Digital-Naturalism-Laboratories/Mothbox_Electronics/Mothbox_PCBs/Mothbox_PCB_5.0.6/MothBox/Adafruit-INA219-Current-Sensor-PCB-master/assets/904.jpg

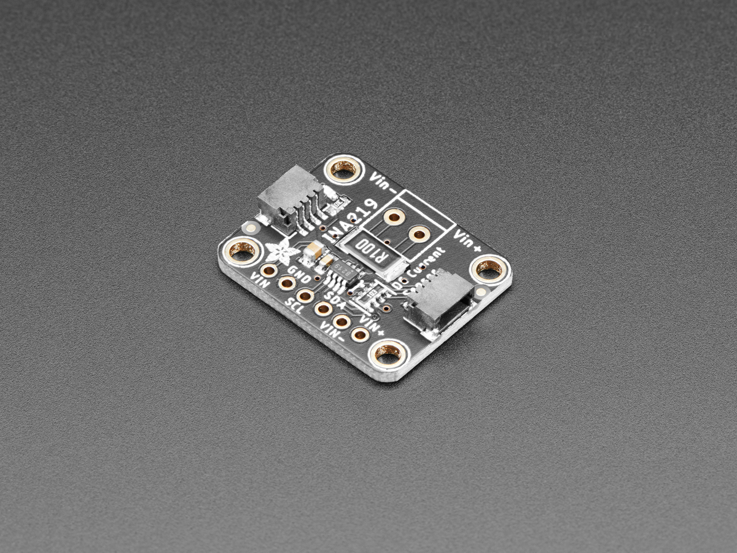
Mothbox_PCBs/Mothbox_PCB_5.0.6/MothBox/Adafruit-INA219-Current-Sensor-PCB-master/assets/904.jpg
