Digital-Naturalism-Laboratories/Mothbox_Electronics/Mothbox_PCBs/Mothbox_PCB_5.0.6/MothBox/graphics/FC5B0830.jpg

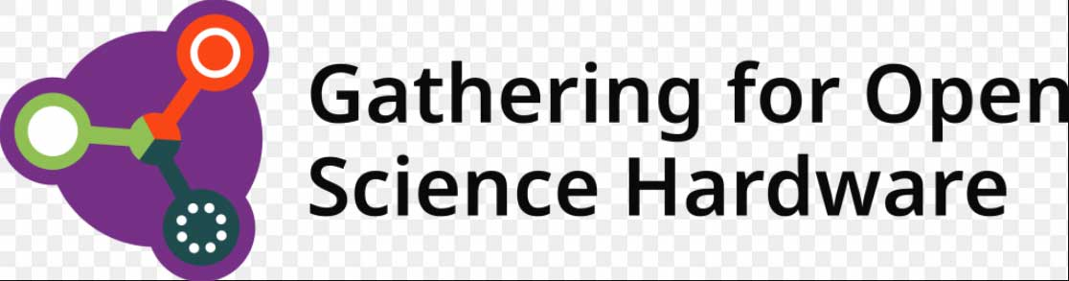
Mothbox_PCBs/Mothbox_PCB_5.0.6/MothBox/graphics/FC5B0830.jpg
