Digital-Naturalism-Laboratories/Mothbox_Electronics/Mothbox_PCBs/Mothbox_PCB_5.0.6/MothBox/Mothbox_5.0.4/MothBox_5.0.3/RPi5-HATplus-master/img/HATPlus_Template_dims.png

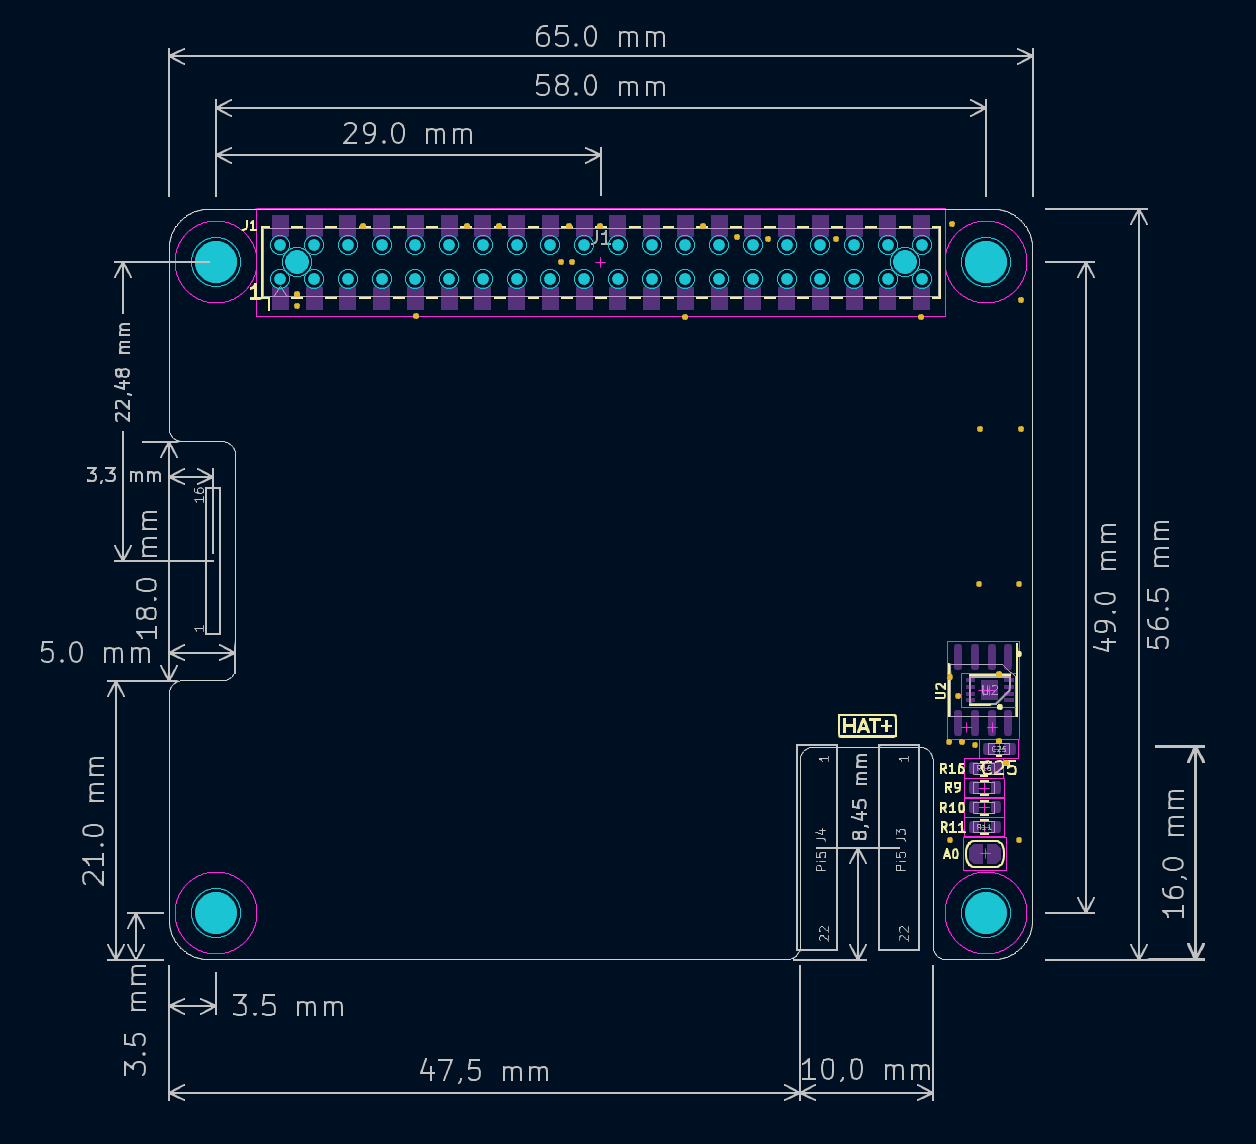
Mothbox_PCBs/Mothbox_PCB_5.0.6/MothBox/Mothbox_5.0.4/MothBox_5.0.3/RPi5-HATplus-master/img/HATPlus_Template_dims.png
