Digital-Naturalism-Laboratories/Mothbox_Electronics/Mothbox_PCBs/reference rotations b.png

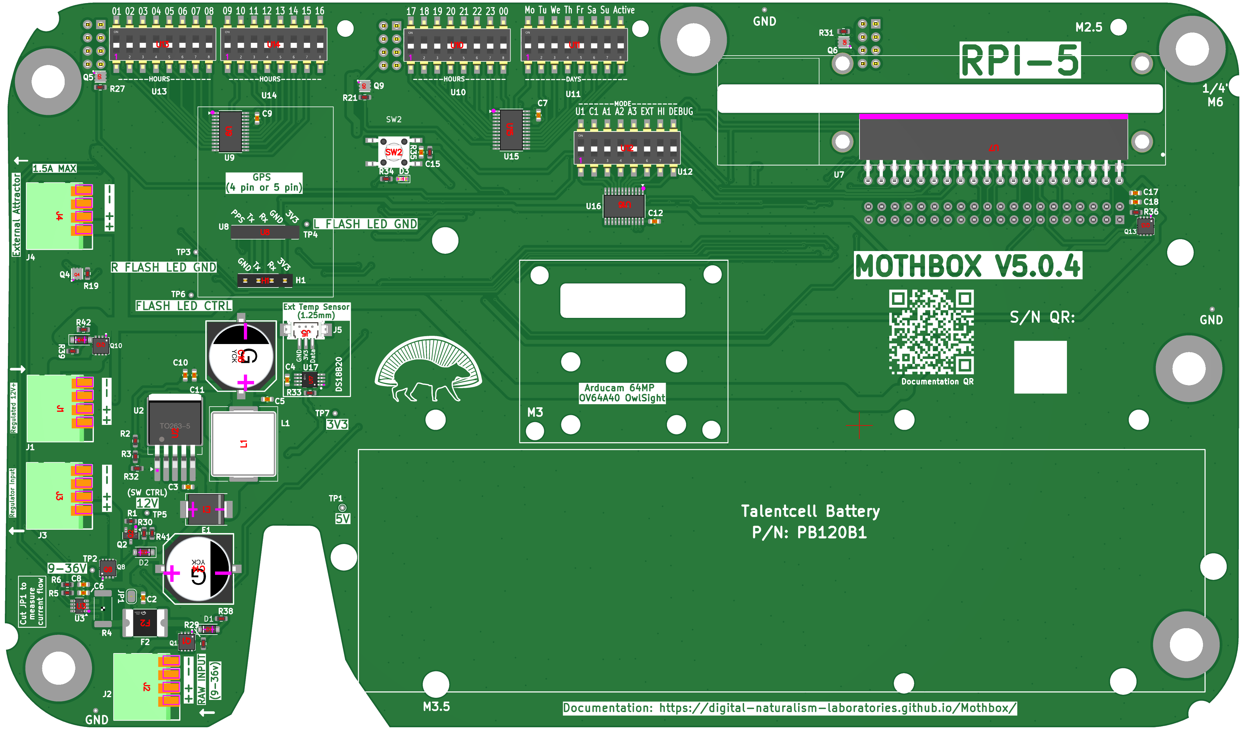
Mothbox_PCBs/reference rotations b.png
