Digital-Naturalism-Laboratories/Mothbox_Electronics/Mothbox_PCBs/reference rotations f.png

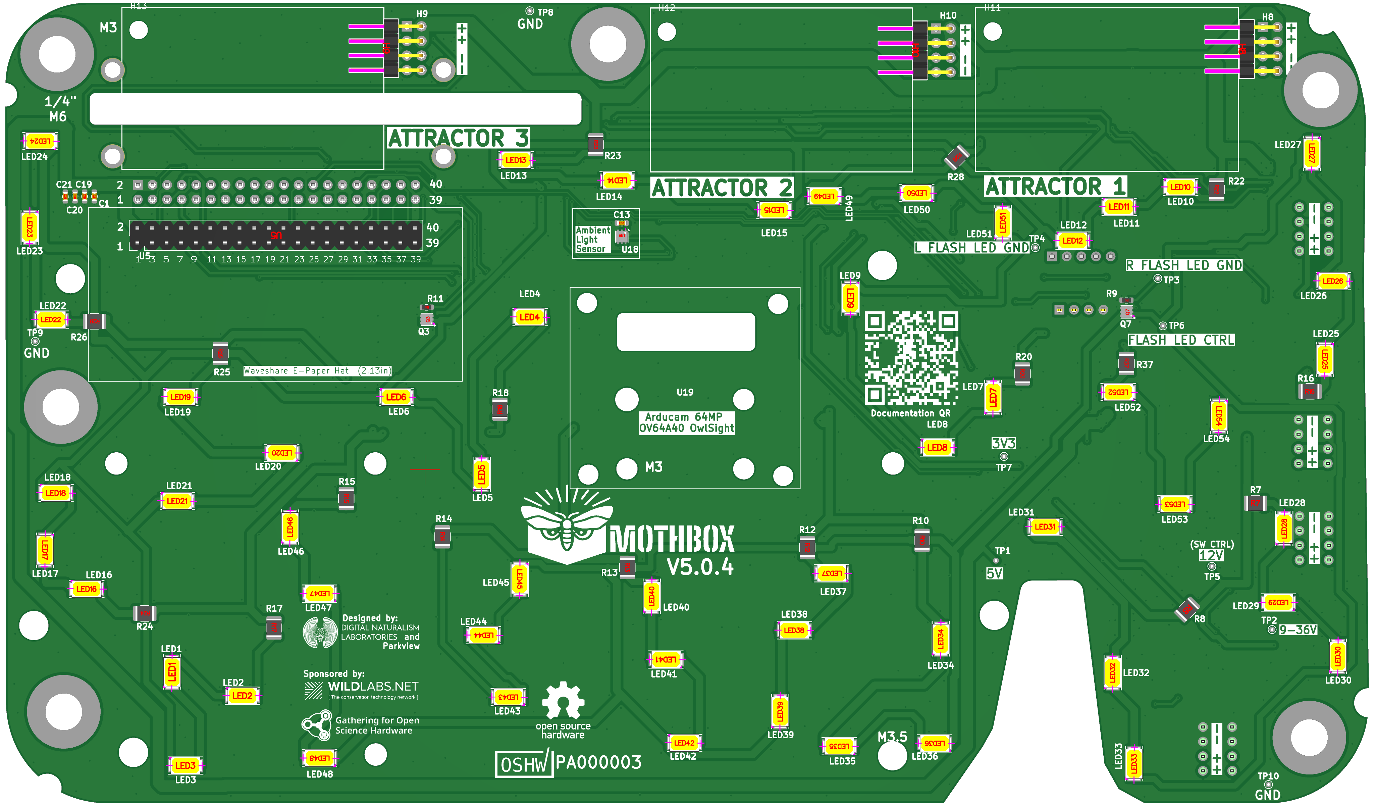
Mothbox_PCBs/reference rotations f.png
